Futuwear-V2/Futuwear-V2/Nettisivu/assets/css/images/backgrounds/18.jpg

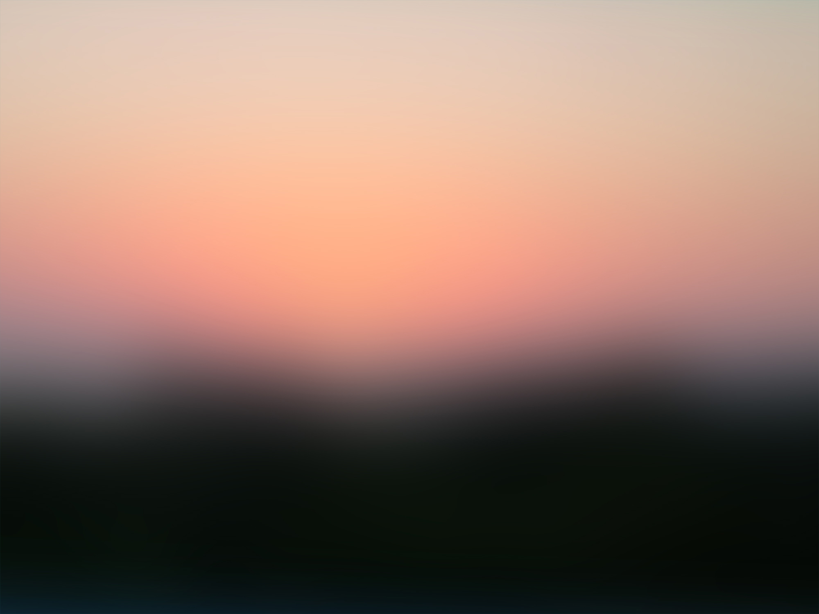
Nettisivu/assets/css/images/backgrounds/18.jpg
