Futuwear-V2/Futuwear-V2/Nettisivu/assets/css/images/backgrounds/30.jpg

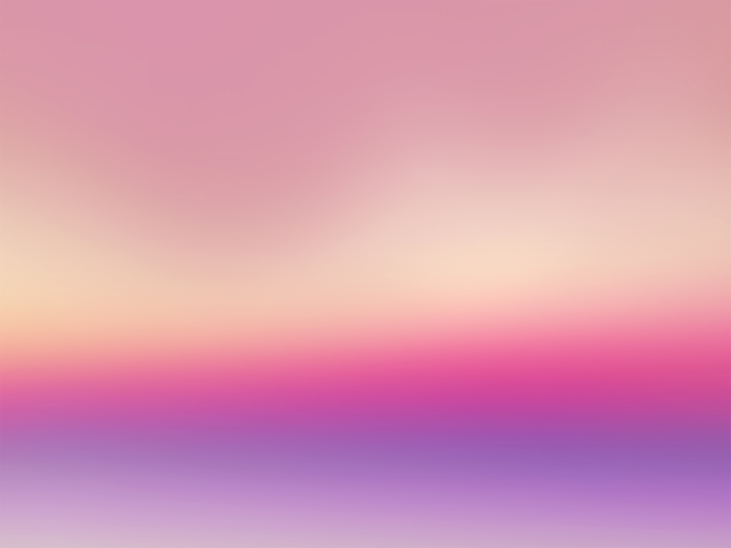
Nettisivu/assets/css/images/backgrounds/30.jpg
