Futuwear-V2/Futuwear-V2/Nettisivu/images/bruce_photo.jpg

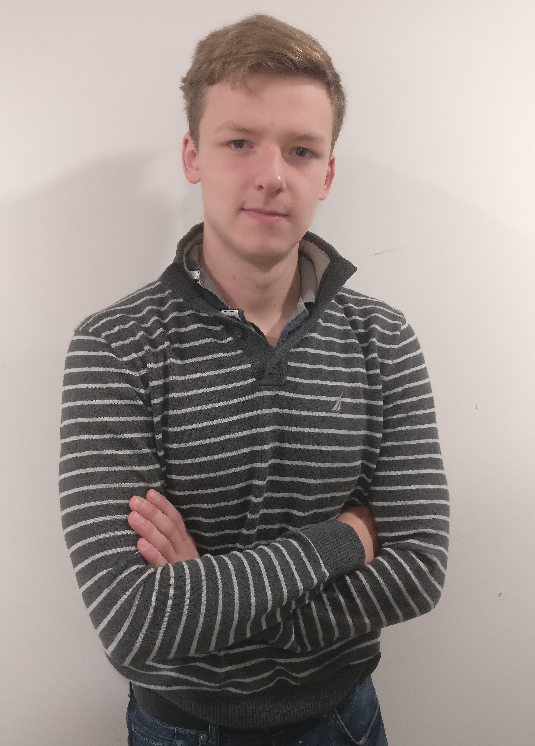
Nettisivu/images/bruce_photo.jpg
