Futuwear-V2/Futuwear-V2/Nettisivu/images/clothing.jpg

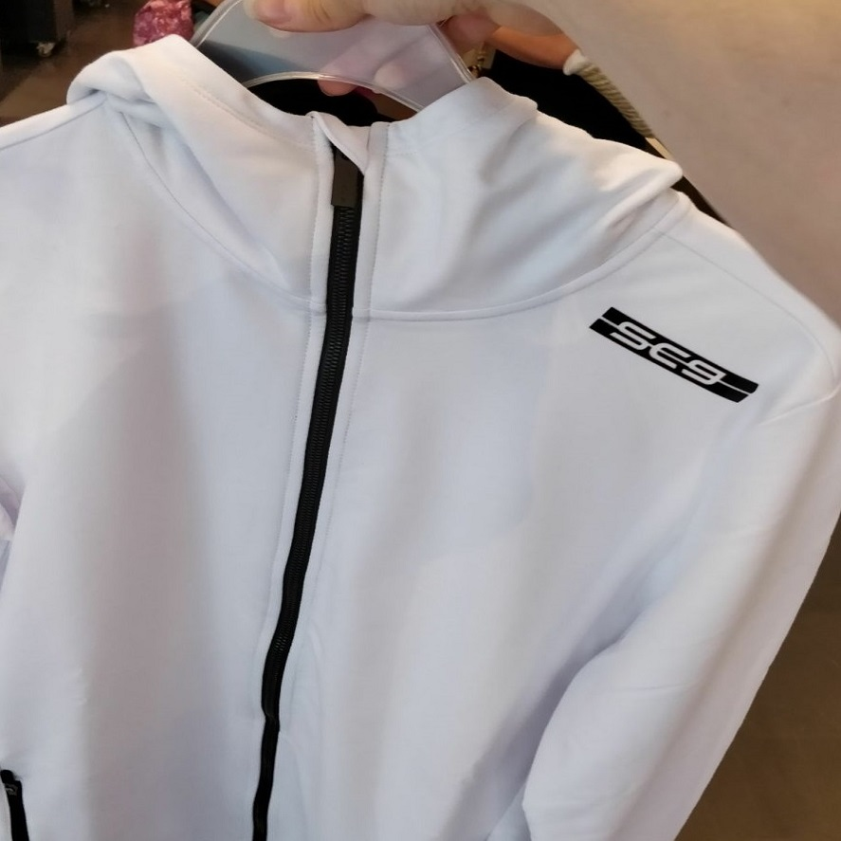
Nettisivu/images/clothing.jpg
