Futuwear-V2/Futuwear-V2/Nettisivu/images/clothing_back.JPG

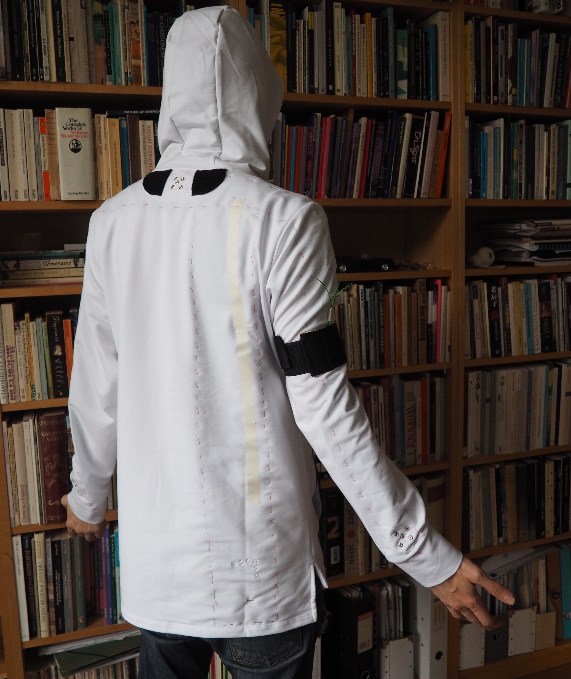
Nettisivu/images/clothing_back.JPG
