Futuwear-V2/Futuwear-V2/Nettisivu/images/elliot_kolhi_photo.jpg

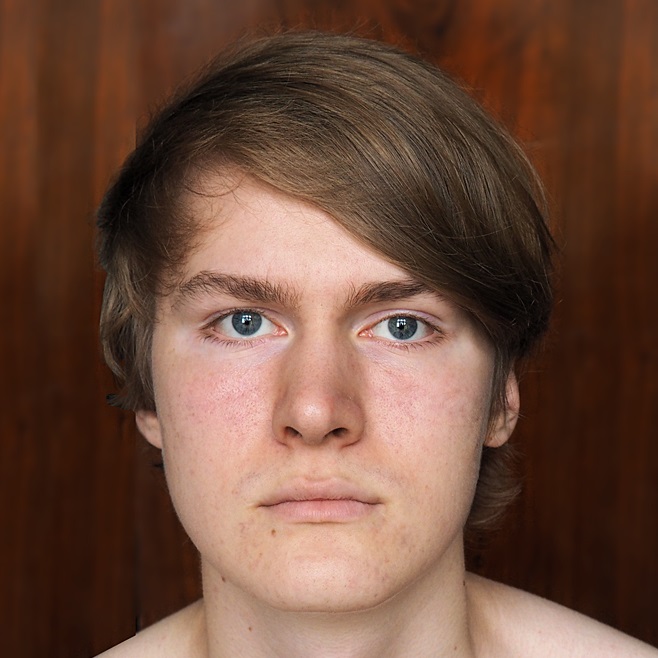
Nettisivu/images/elliot_kolhi_photo.jpg
