Futuwear-V2/Futuwear-V2/Nettisivu/images/elliot_photo.jpg

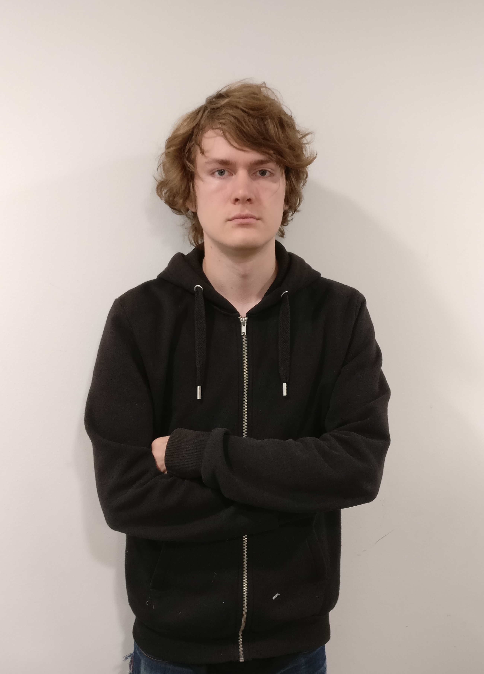
Nettisivu/images/elliot_photo.jpg
