Futuwear-V2/Futuwear-V2/Nettisivu/images/ESP32_WROOM_Module.jpg

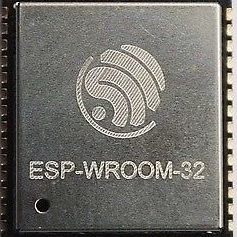
Nettisivu/images/ESP32_WROOM_Module.jpg
