Futuwear-V2/Futuwear-V2/Nettisivu/images/futuwear_v1.png

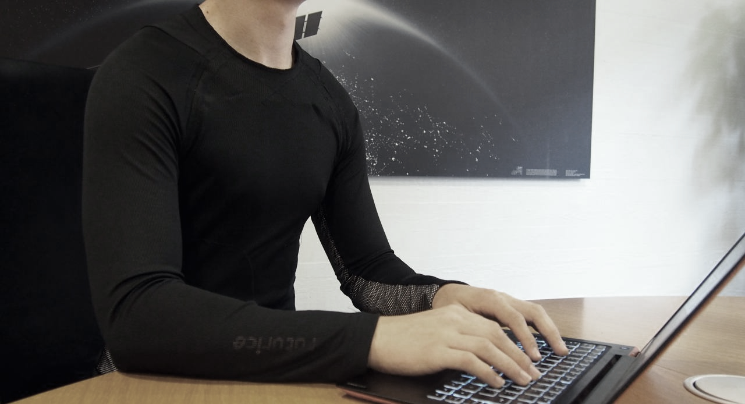
Nettisivu/images/futuwear_v1.png
