Futuwear-V2/Futuwear-V2/Nettisivu/images/imu_case.jpg

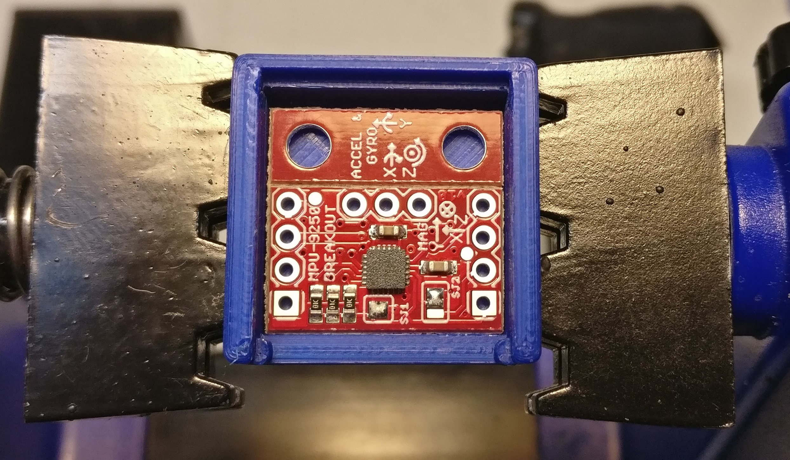
Nettisivu/images/imu_case.jpg
