Futuwear-V2/Futuwear-V2/Nettisivu/images/imu_case_closed.jpg

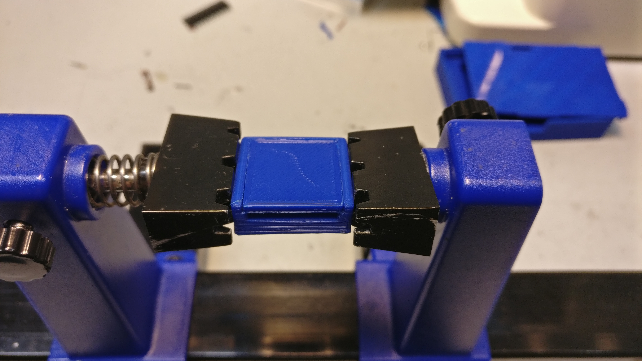
Nettisivu/images/imu_case_closed.jpg
