Futuwear-V2/Futuwear-V2/Nettisivu/images/imu_pouch.jpg

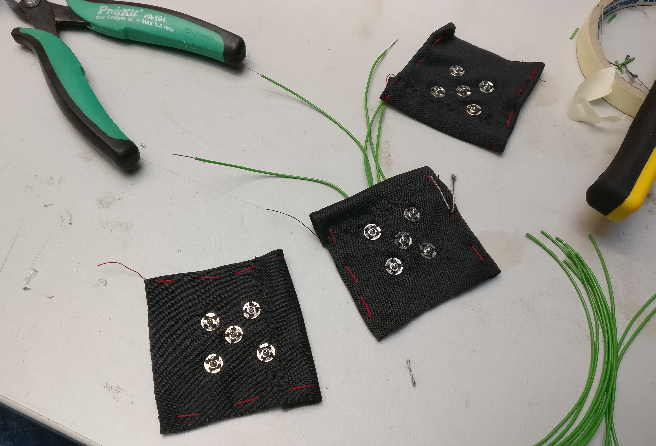
Nettisivu/images/imu_pouch.jpg
