Futuwear-V2/Futuwear-V2/Nettisivu/images/jere_photo.jpg

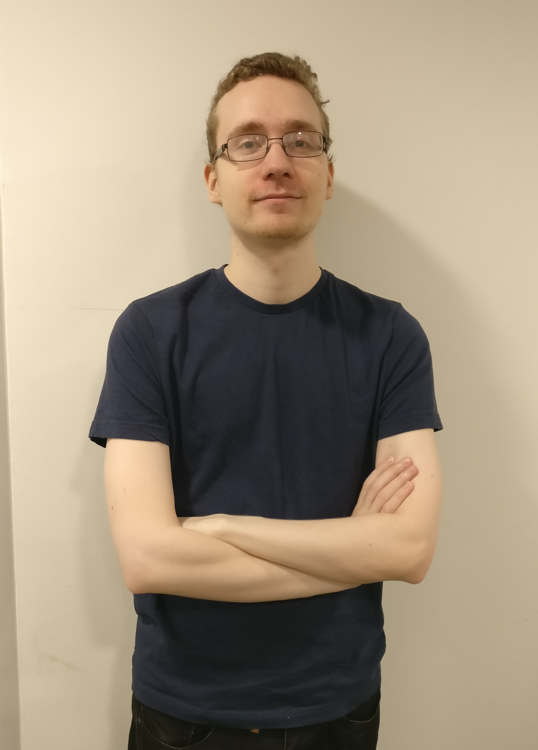
Nettisivu/images/jere_photo.jpg
