Futuwear-V2/Futuwear-V2/Nettisivu/images/mcu_finished_front.jpg

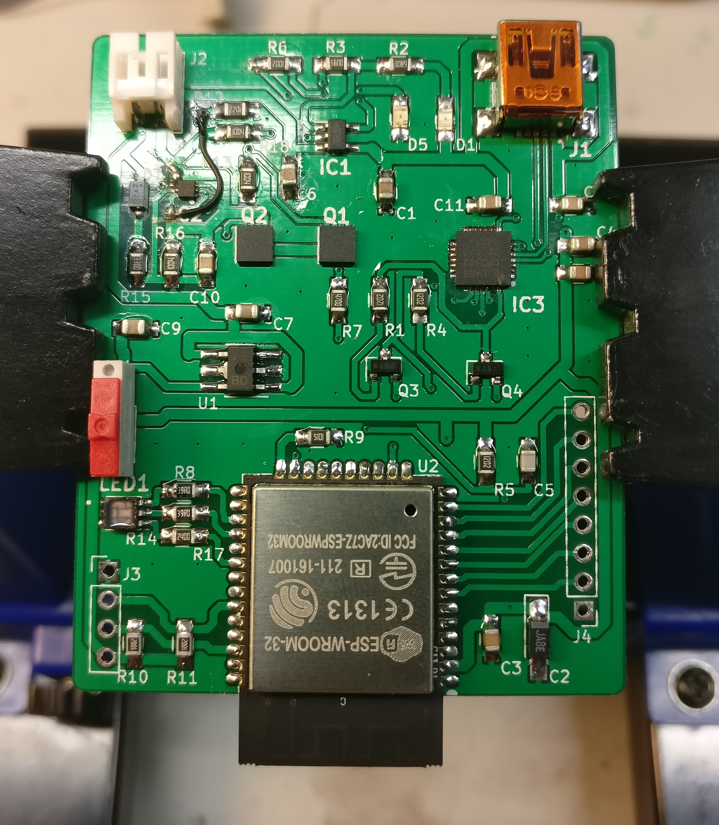
Nettisivu/images/mcu_finished_front.jpg
