Futuwear-V2/Futuwear-V2/Nettisivu/images/mpu_9250_grey.jpg

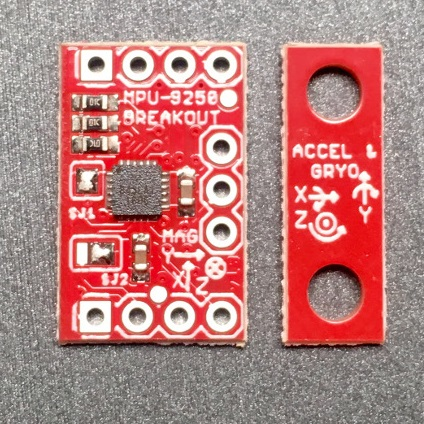
Nettisivu/images/mpu_9250_grey.jpg
