Futuwear-V2/Futuwear-V2/Nettisivu/images/pcb_case_front.jpg

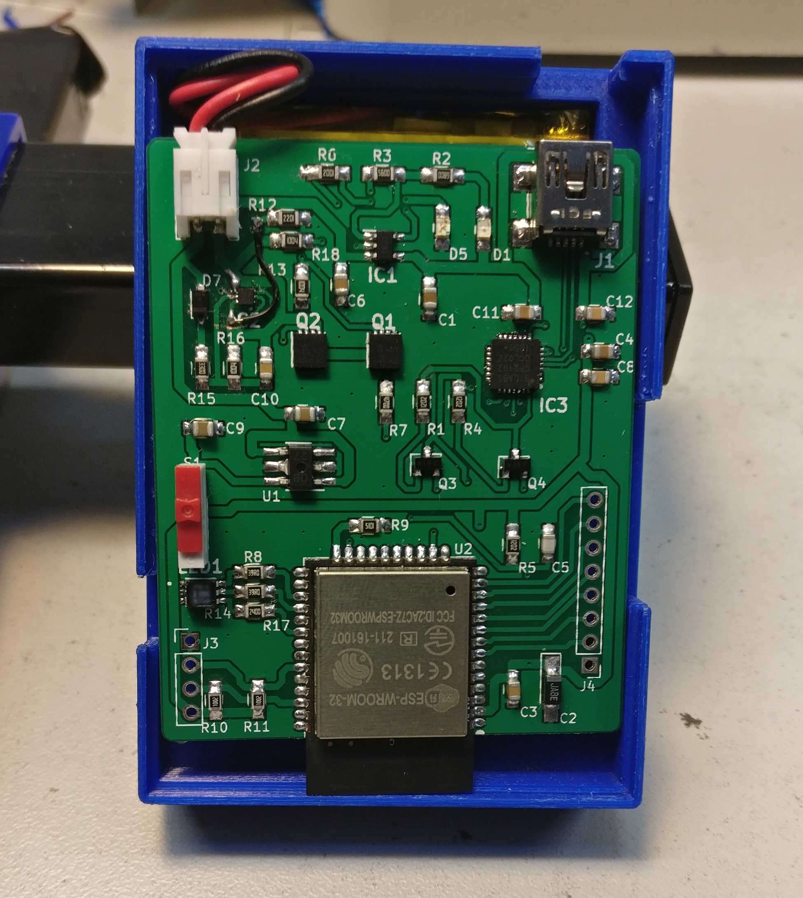
Nettisivu/images/pcb_case_front.jpg
