Futuwear-V2/Futuwear-V2/Nettisivu/images/PCB_Front_landscape.jpg

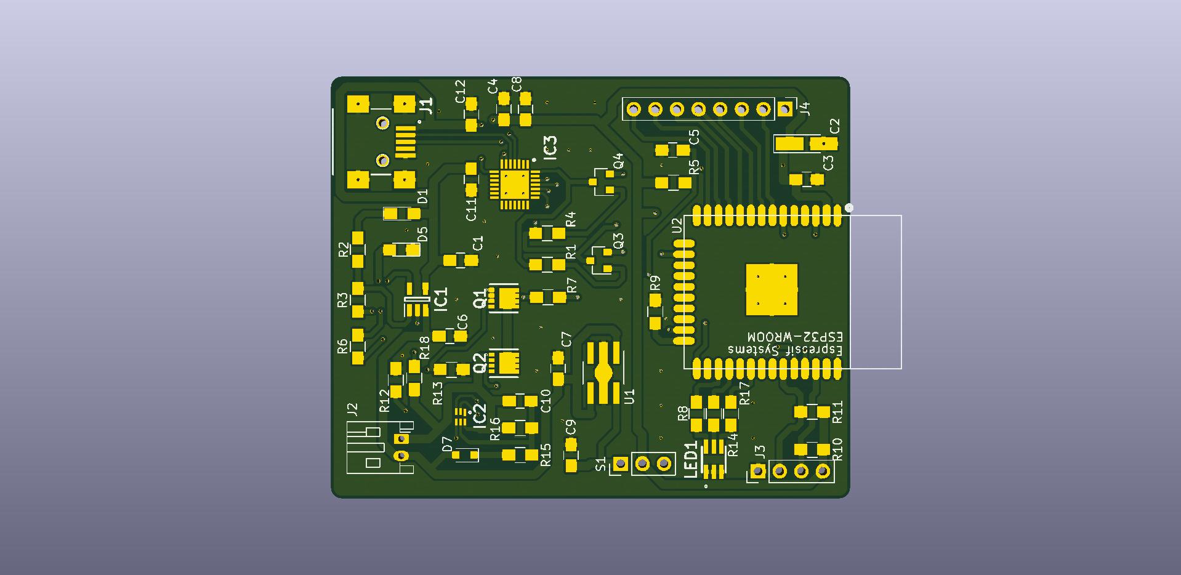
Nettisivu/images/PCB_Front_landscape.jpg
