Futuwear-V2/Futuwear-V2/Nettisivu/images/torso_interface.png

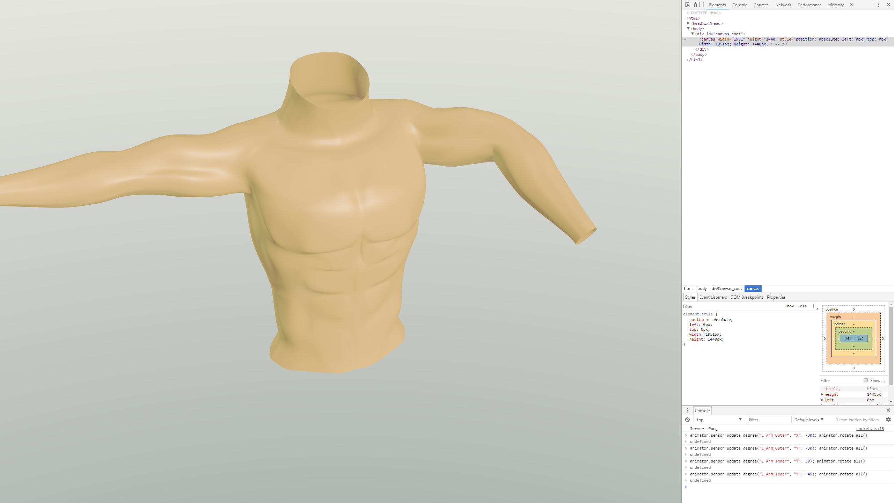
Nettisivu/images/torso_interface.png
