Futuwear-V2/Futuwear-V2/Nettisivu/images/torso_square.png

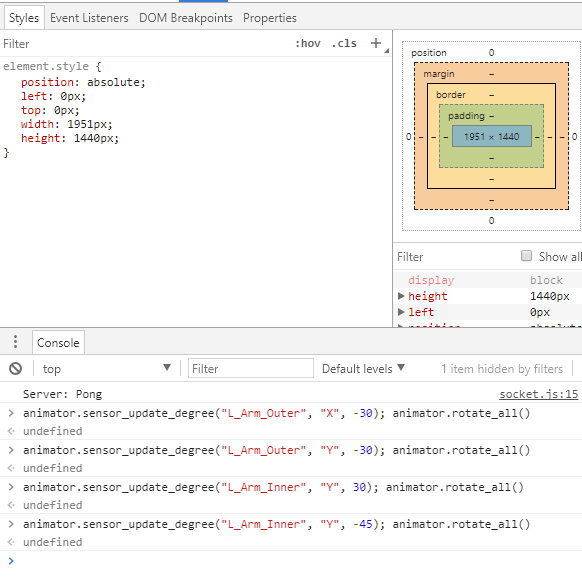
Nettisivu/images/torso_square.png
